totodd/RoomEscape/module/Daniel/newPhone/色盲1/1.bmp

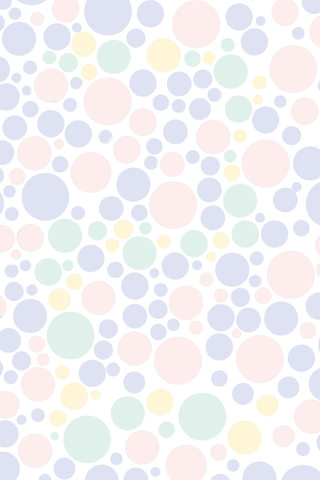
module/Daniel/newPhone/色盲1/1.bmp
