totodd/RoomEscape/module/Daniel/newPhone/色盲1/2.bmp

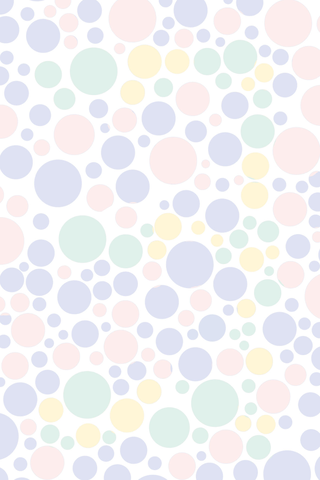
module/Daniel/newPhone/色盲1/2.bmp
