totodd/RoomEscape/module/Daniel/newPhone/色盲1/3.bmp

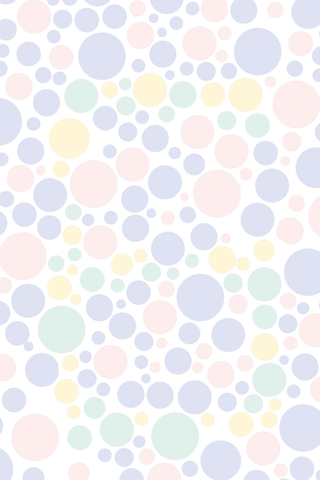
module/Daniel/newPhone/色盲1/3.bmp
