totodd/RoomEscape/module/Daniel/newPhone/色盲1/73mirror.bmp

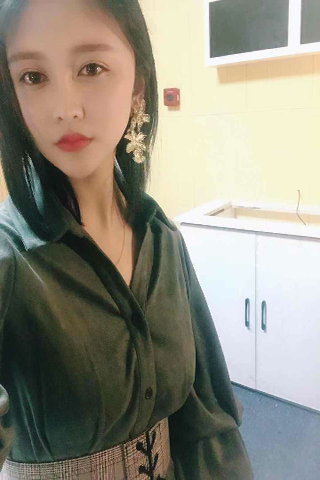
module/Daniel/newPhone/色盲1/73mirror.bmp
