totodd/RoomEscape/module/Daniel/newPhone/色盲1/充电中2.bmp

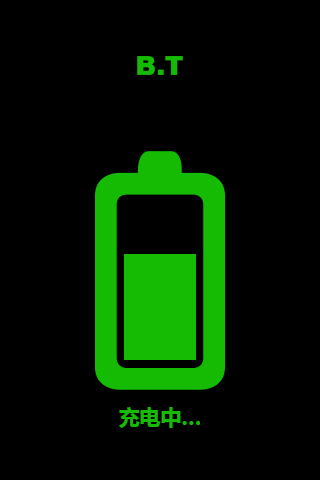
module/Daniel/newPhone/色盲1/充电中2.bmp
