totodd/RoomEscape/module/Daniel/newPhone/色盲1/开机界面.bmp

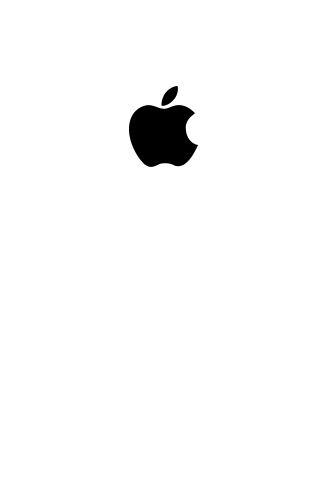
module/Daniel/newPhone/色盲1/开机界面.bmp
