totodd/RoomEscape/module/Daniel/newPhone/色盲1/来电界面.bmp

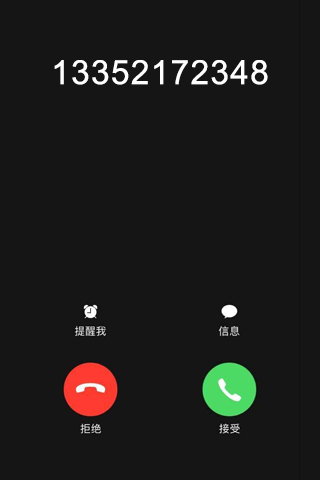
module/Daniel/newPhone/色盲1/来电界面.bmp
