totodd/RoomEscape/module/Daniel/newPhone/色盲1/短信界面.bmp

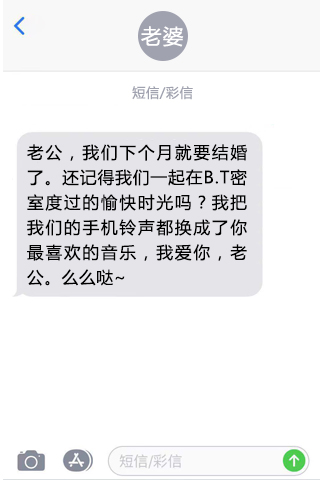
module/Daniel/newPhone/色盲1/短信界面.bmp
