totodd/RoomEscape/module/Daniel/newPhone/色盲1/通话界面.bmp

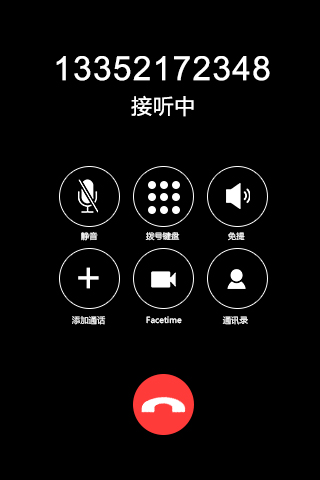
module/Daniel/newPhone/色盲1/通话界面.bmp
