totodd/RoomEscape/module/faceRecog/15731544851680_.pic.jpg

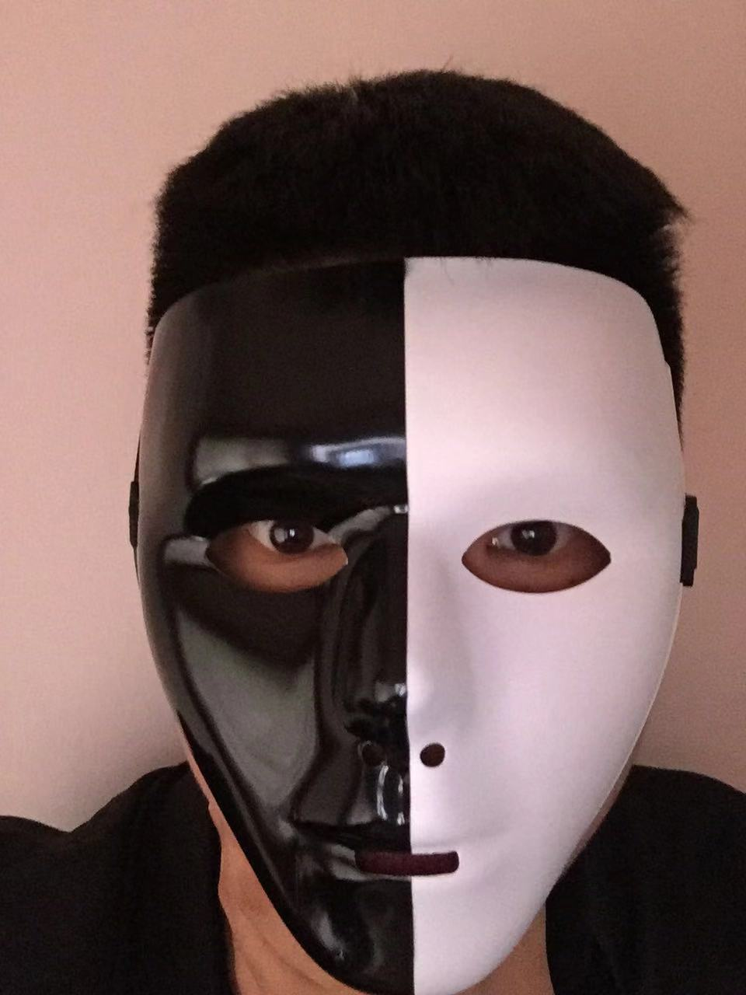
module/faceRecog/15731544851680_.pic.jpg
