totodd/RoomEscape/module/faceRecog/15761544852548_.pic.jpg

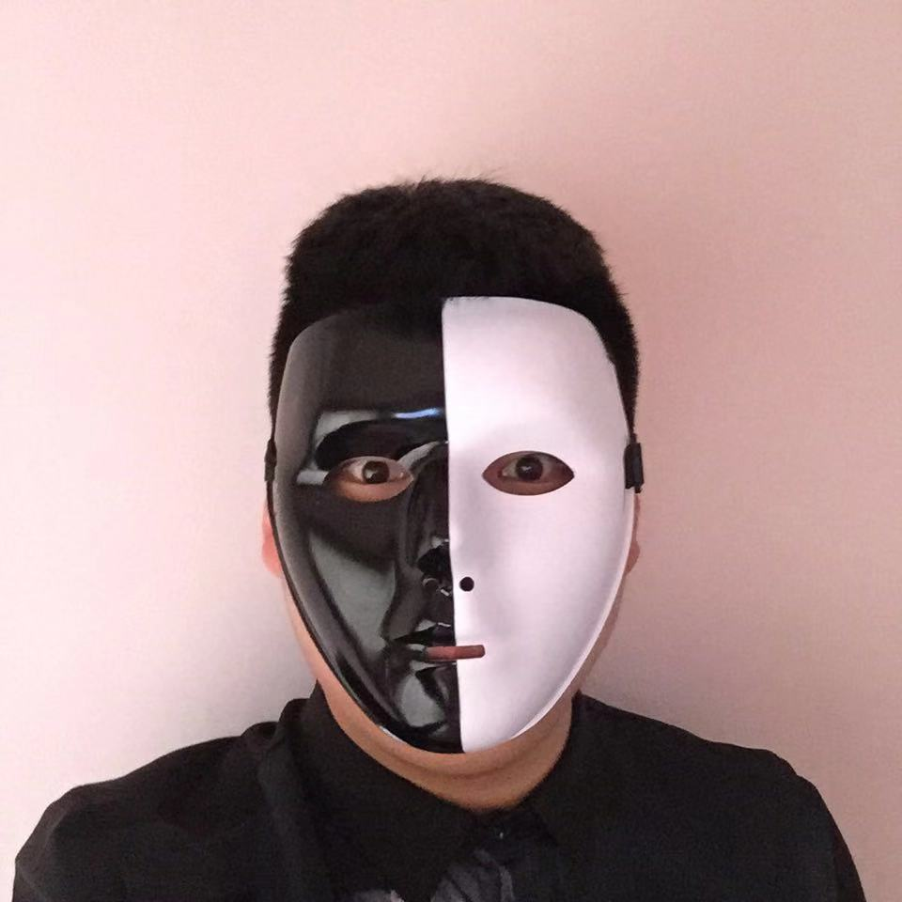
module/faceRecog/15761544852548_.pic.jpg
