totodd/RoomEscape/module/faceRecog/15771544852557_.pic.jpg

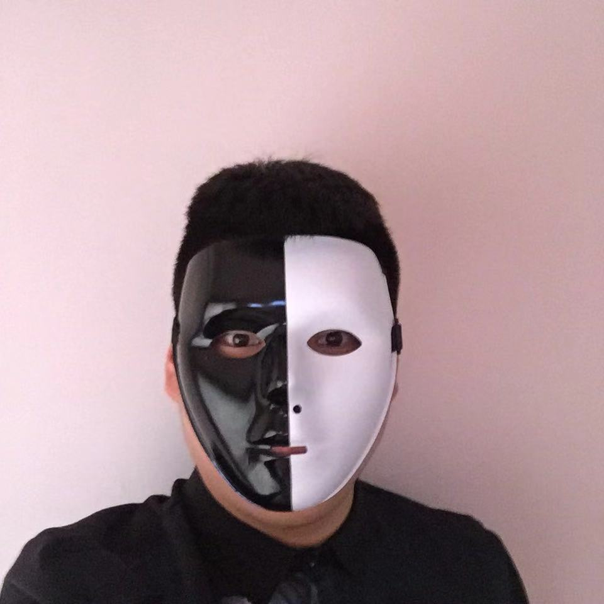
module/faceRecog/15771544852557_.pic.jpg
