totodd/RoomEscape/module/faceRecog/15821544867200_.pic.jpg

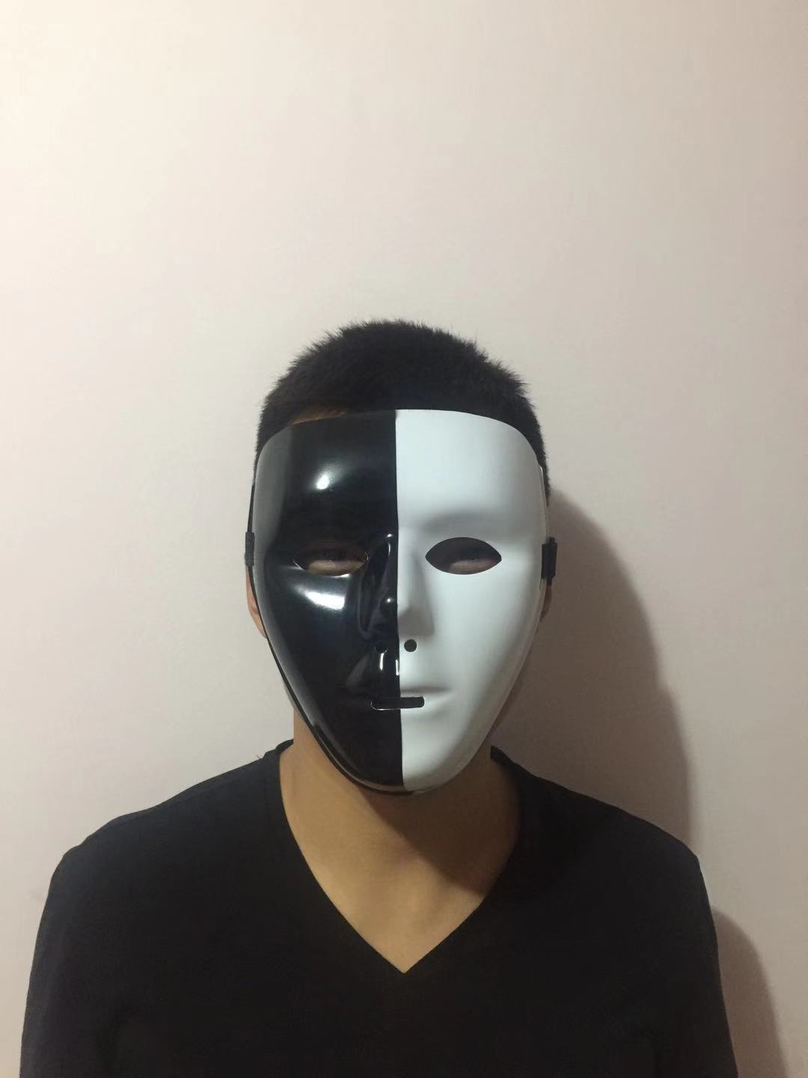
module/faceRecog/15821544867200_.pic.jpg
