totodd/RoomEscape/module/faceRecog/15831544867201_.pic.jpg

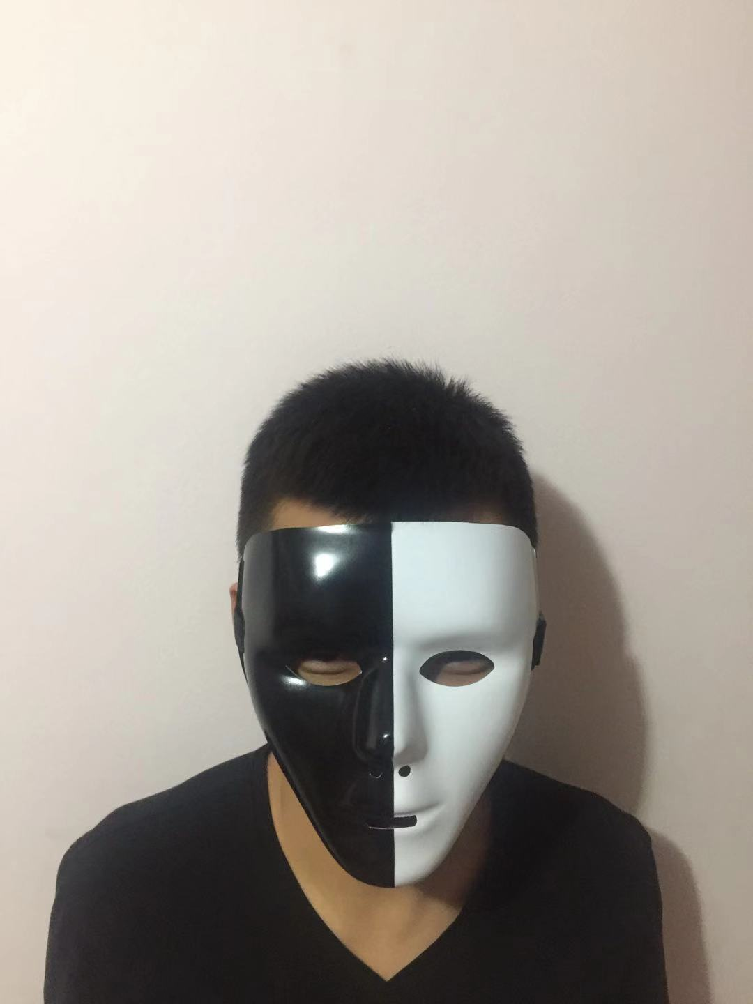
module/faceRecog/15831544867201_.pic.jpg
