totodd/RoomEscape/module/faceRecog/15841544867201_.pic.jpg

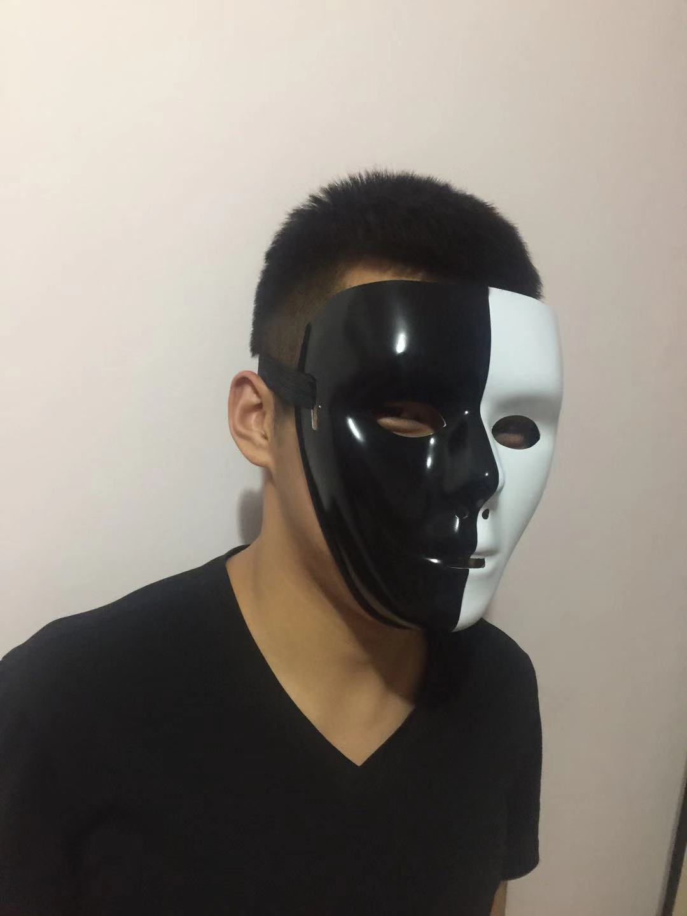
module/faceRecog/15841544867201_.pic.jpg
