totodd/RoomEscape/module/faceRecog/15851544867202_.pic.jpg

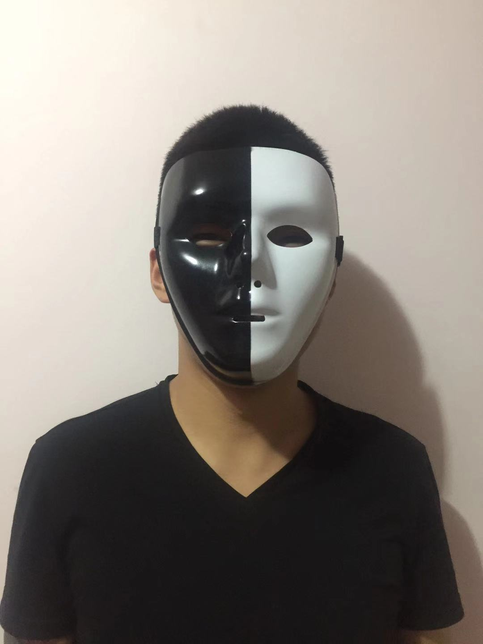
module/faceRecog/15851544867202_.pic.jpg
