totodd/RoomEscape/module/faceRecog/15861544867202_.pic.jpg

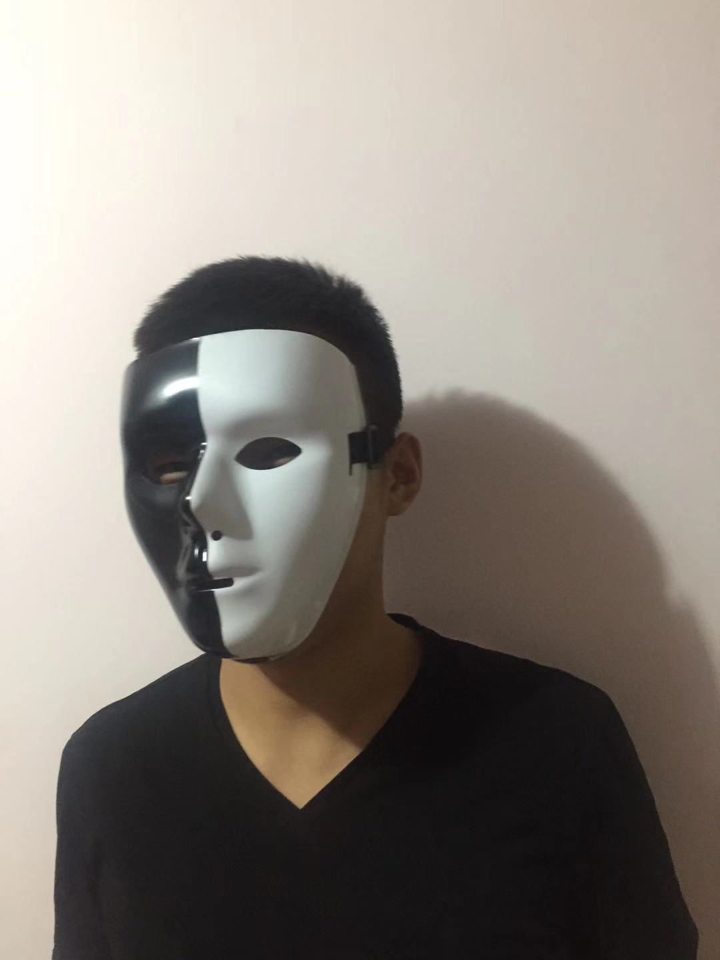
module/faceRecog/15861544867202_.pic.jpg
