totodd/RoomEscape/module/faceRecog/15881544867203_.pic.jpg

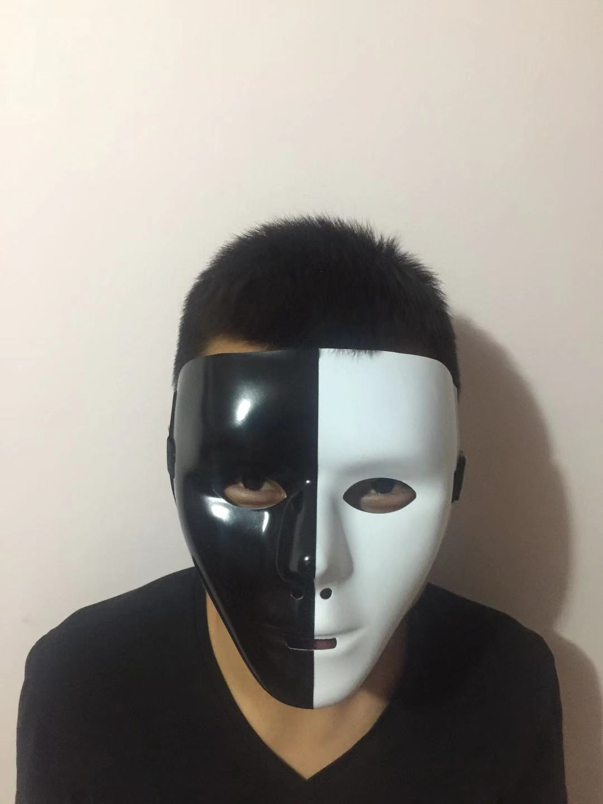
module/faceRecog/15881544867203_.pic.jpg
