totodd/RoomEscape/module/faceRecog/15891544867204_.pic.jpg

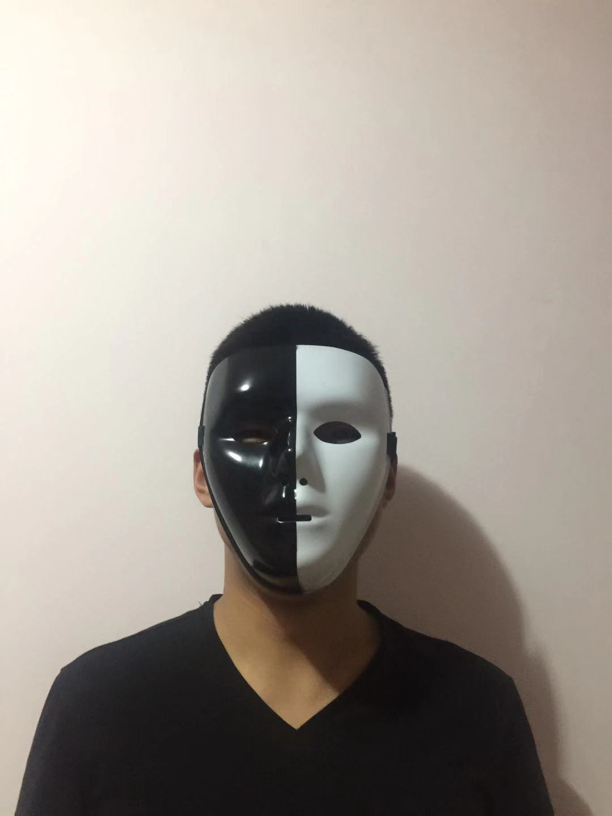
module/faceRecog/15891544867204_.pic.jpg
