totodd/RoomEscape/module/faceRecog/15901544867204_.pic.jpg

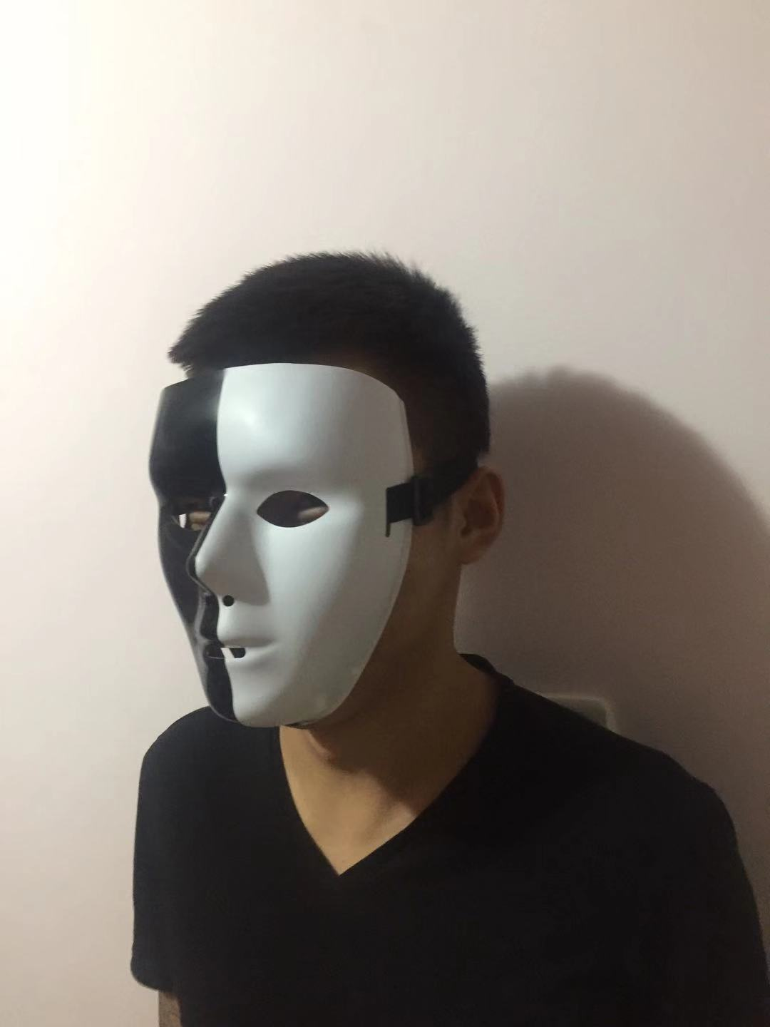
module/faceRecog/15901544867204_.pic.jpg
